AbiesDSP/ProtoDAC/ProtoDAC.cydsn/logger.c

#include "logger.h"
#include "rtc.h"

#include <string.h>
#include <stdio.h>
#include <stdlib.h>
#include <stdarg.h>

#include "cptr.h"

#include "project_config.h"

const char *log_level_strs[] = {
    "TRACE",
    "DEBUG",
    "INFO ",
    "WARN ",
    "ERROR",
};
static inline const char *log_level2str(enum LogLevel level)
{
    return log_level_strs[level];
}

int log_handler_init_funcs(LogHandler *handler, LogHandlerWrite write, LogHandlerRead read)
{
    handler->write = write;
    handler->read = read;

    return 0;
}

/*  */
const char *default_header_fmt_str = "[%s : %s : %d] - ";

void logger_init(Logger *log, LogHandler *handler, LogHeaderFormat header_format, LogArgsFormat args_format, const char *header_fmt_str)
{
    log->n_handlers = 0;

    if (handler != NULL)
    {
        log->handlers[log->n_handlers] = handler;
        log->n_handlers++;
    }
    if (header_format == NULL)
    {
        log->header_format = sprintf;
    }
    if (args_format == NULL)
    {
        log->args_format = vsprintf;
    }
    if (header_fmt_str == NULL)
    {
        log->header_fmt_str = default_header_fmt_str;
    }

    log->level = LOG_ERROR;
}

int logger_add_handler(Logger *log, LogHandler *handler)
{
    if (log->n_handlers < LOG_MAX_HANDLERS)
    {
        log->handlers[log->n_handlers] = handler;
        log->n_handlers++;
        return 1;
    }
    return 0;
}

// Allocate a temporary block of memory for processing the message.
static char message_buf[LOG_MESSAGE_BUF_SIZE];

void log_(const Logger *log, enum LogLevel level, const char *source_file, const char *args_fmt, ...)
{
    if (level >= GLOBAL_LOG_LEVEL && level >= log->level)
    {
        va_list args;
        va_start(args, args_fmt);
        // Format into the message buffer.
        // Format header
        // level, source_file, timestamp,
        int message_size = log->header_format(message_buf, log->header_fmt_str, log_level2str(level), source_file, rtc_get_time());
        // Format args
        message_size += log->args_format(message_buf + message_size, args_fmt, args);

        for (int i = 0; i < log->n_handlers; i++)
        {
            log->handlers[i]->write(log->handlers[i], message_buf, message_size);
        }

        va_end(args);
    }
}
